PhilipLykov/LimeSDRCase/images/1778969445349.jpg

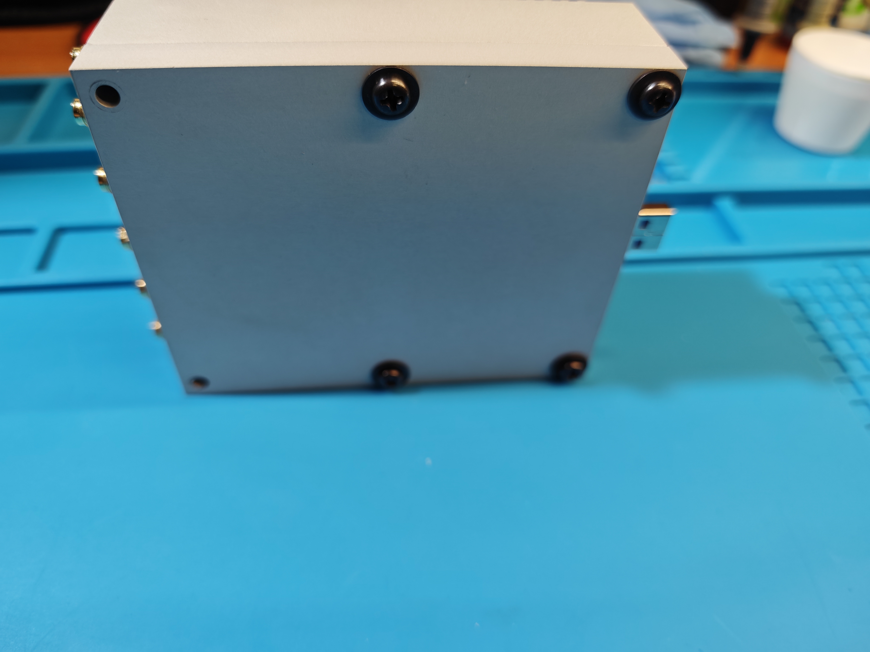
images/1778969445349.jpg
