PhilipLykov/LimeSDRCase/images/1778969445375.jpg

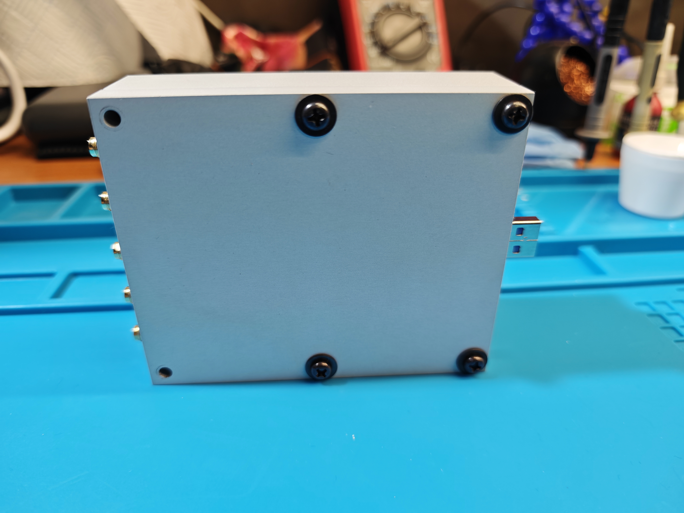
images/1778969445375.jpg
