PhilipLykov/LimeSDRCase/images/1778969445397.jpg

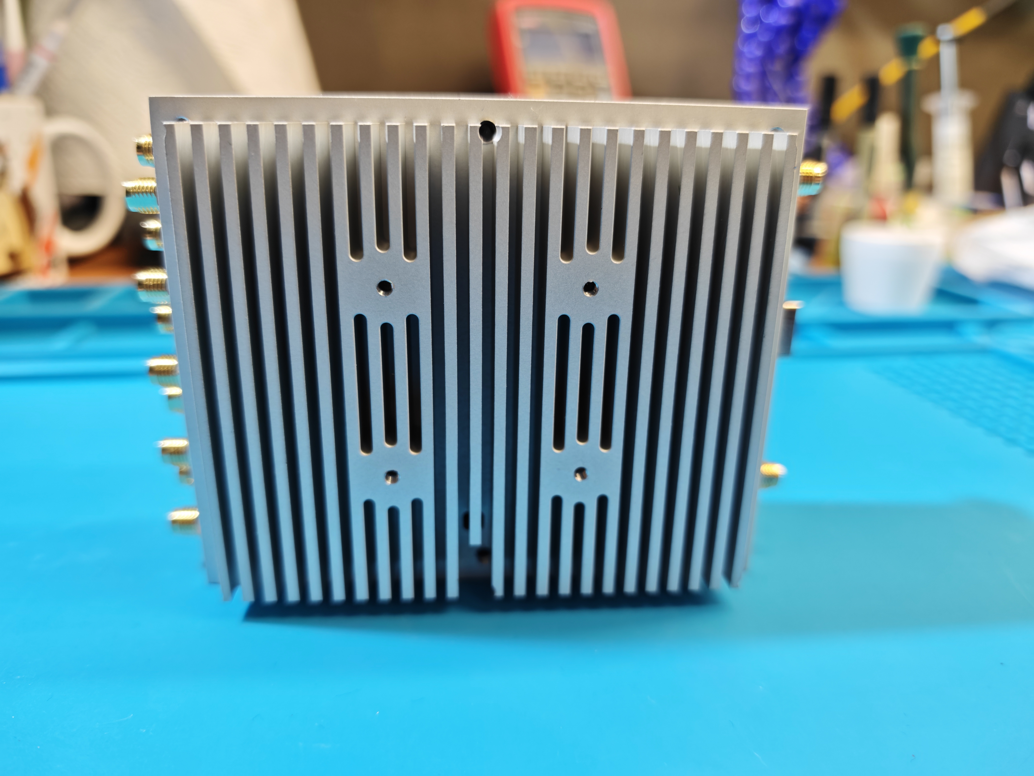
images/1778969445397.jpg
