PhilipLykov/LimeSDRCase/images/1778969445446.jpg

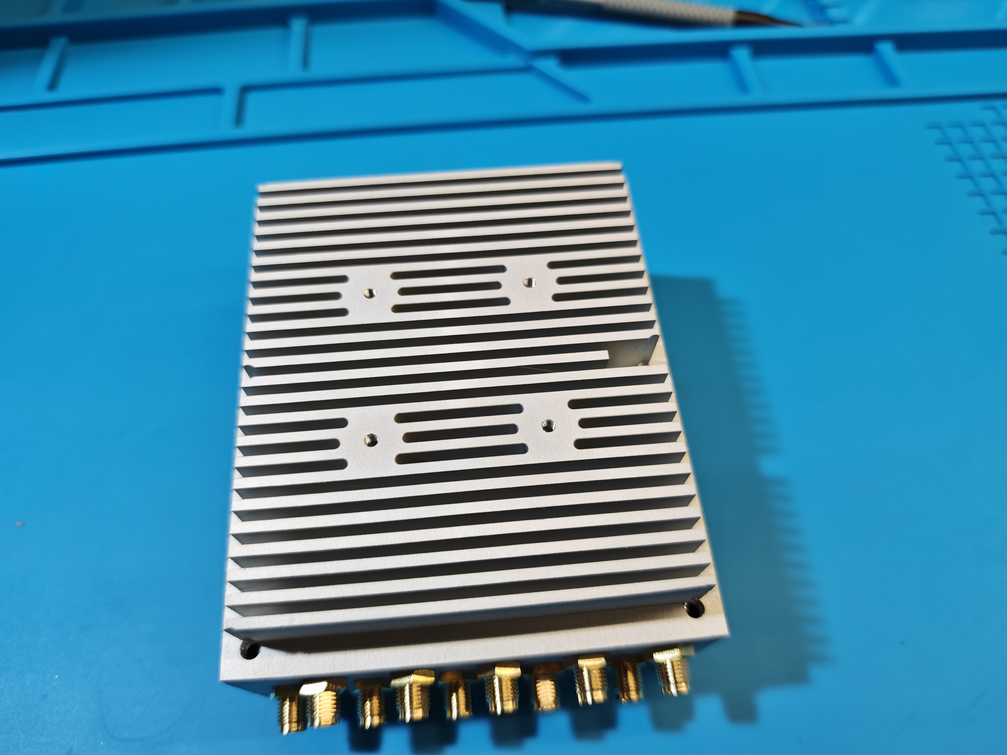
images/1778969445446.jpg
