PhilipLykov/LimeSDRCase/images/1778969445494.jpg

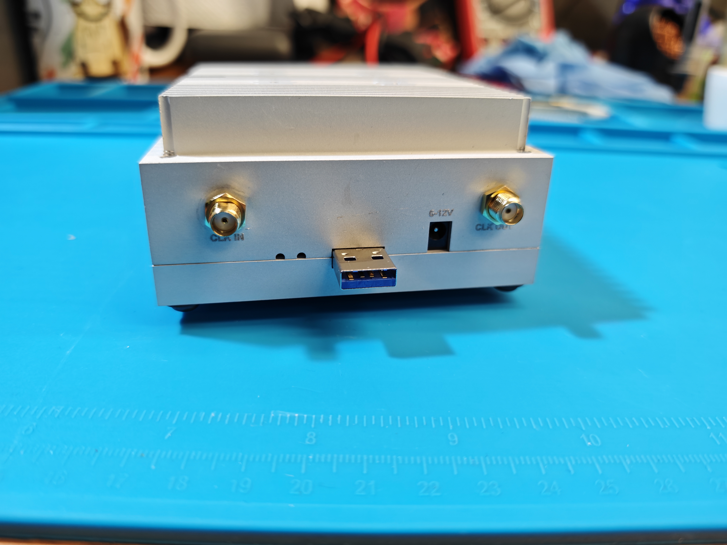
images/1778969445494.jpg
