PhilipLykov/LimeSDRCase/images/1778969445562.jpg

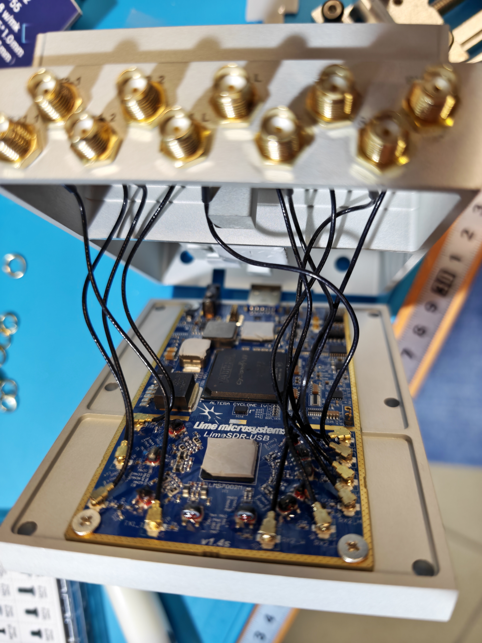
images/1778969445562.jpg
