PhilipLykov/LimeSDRCase/images/1778969445588.jpg

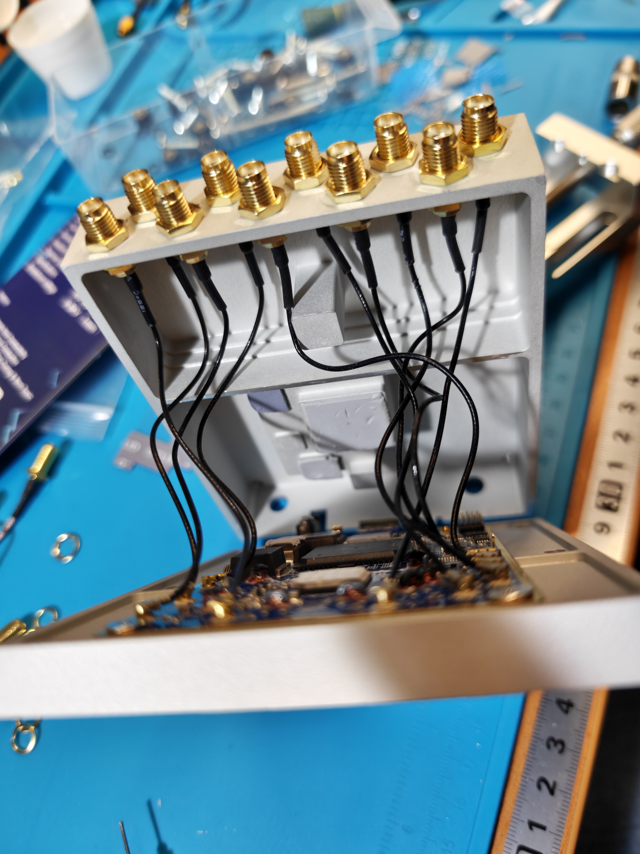
images/1778969445588.jpg
