PhilipLykov/LimeSDRCase/images/1778969445642.jpg

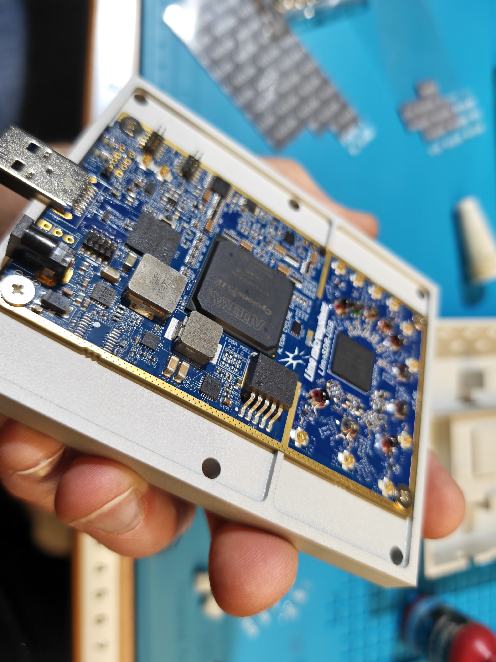
images/1778969445642.jpg
