PhilipLykov/LimeSDRCase/images/1778969445668.jpg

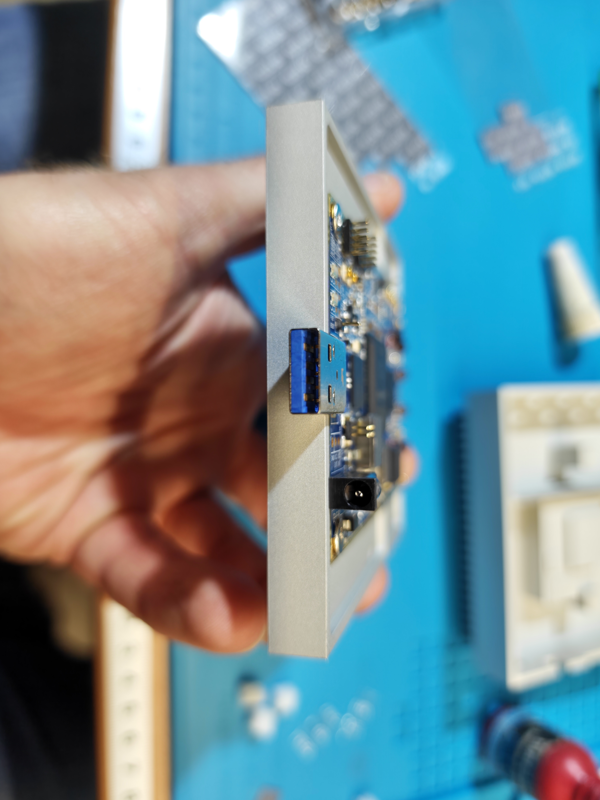
images/1778969445668.jpg
