PhilipLykov/LimeSDRCase/images/1778969445693.jpg

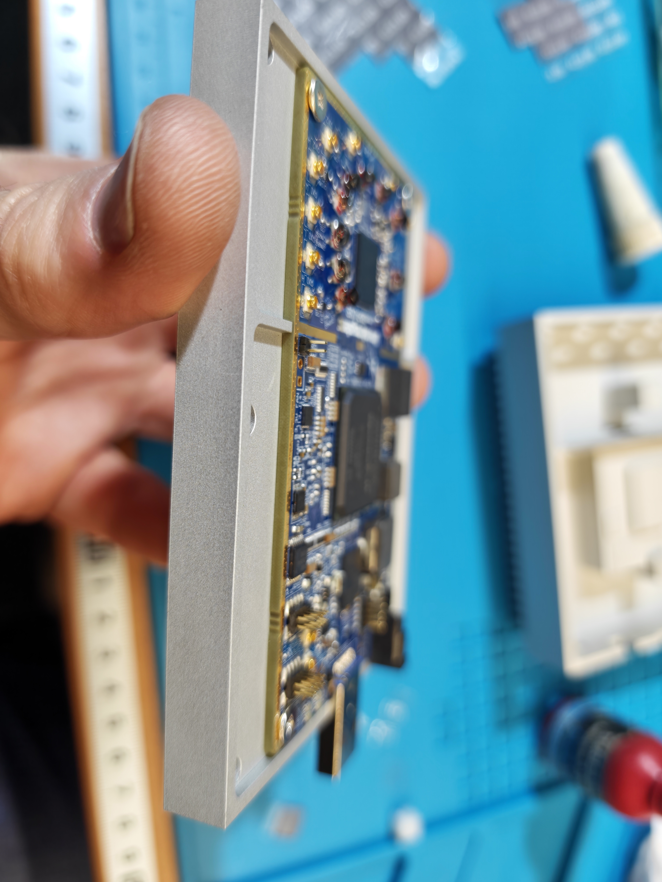
images/1778969445693.jpg
