PhilipLykov/LimeSDRCase/images/1778969445718.jpg

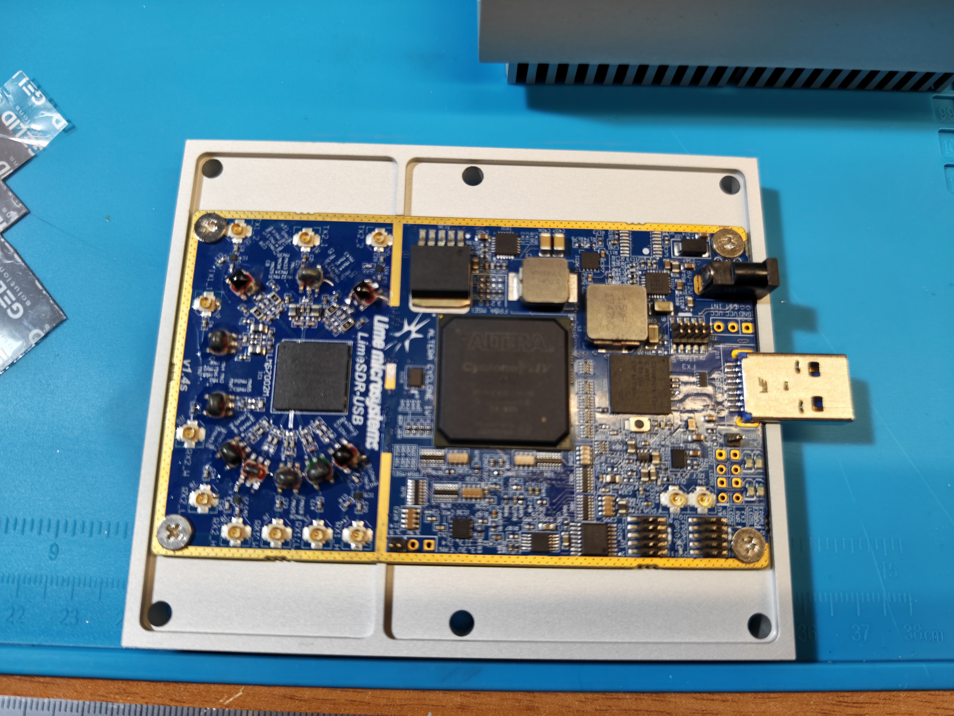
images/1778969445718.jpg
