PhilipLykov/LimeSDRCase/images/1778969445789.jpg

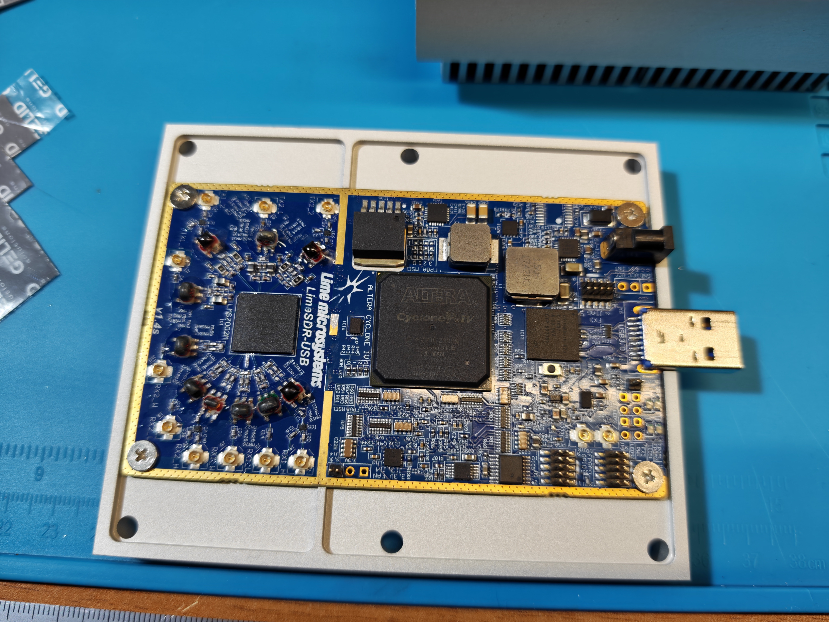
images/1778969445789.jpg
