PhilipLykov/LimeSDRCase/images/1778969445815.jpg

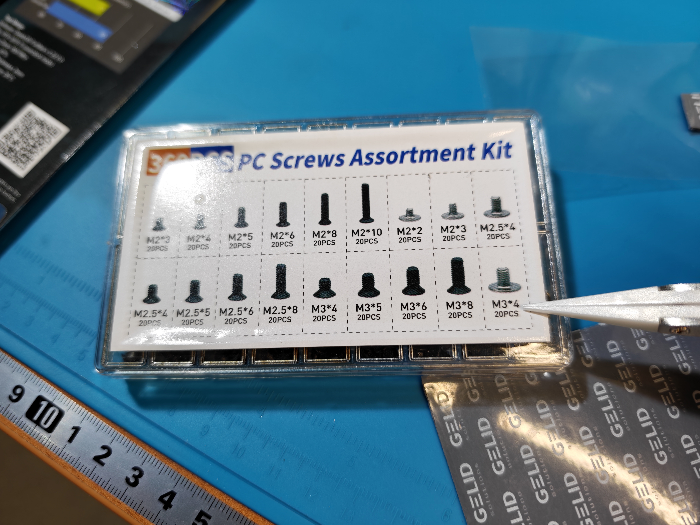
images/1778969445815.jpg
