PhilipLykov/LimeSDRCase/images/1778969445856.jpg

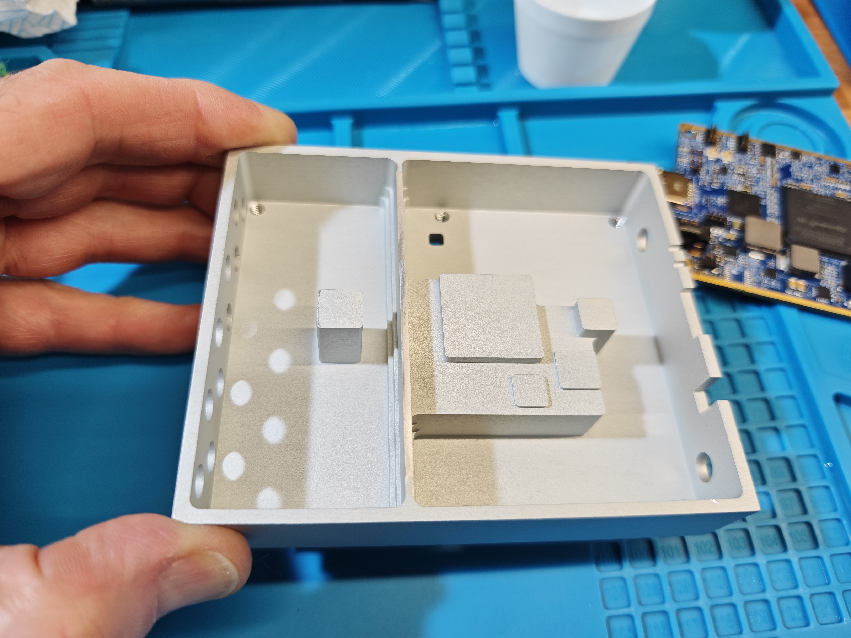
images/1778969445856.jpg
