PhilipLykov/LimeSDRCase/images/1778969445876.jpg

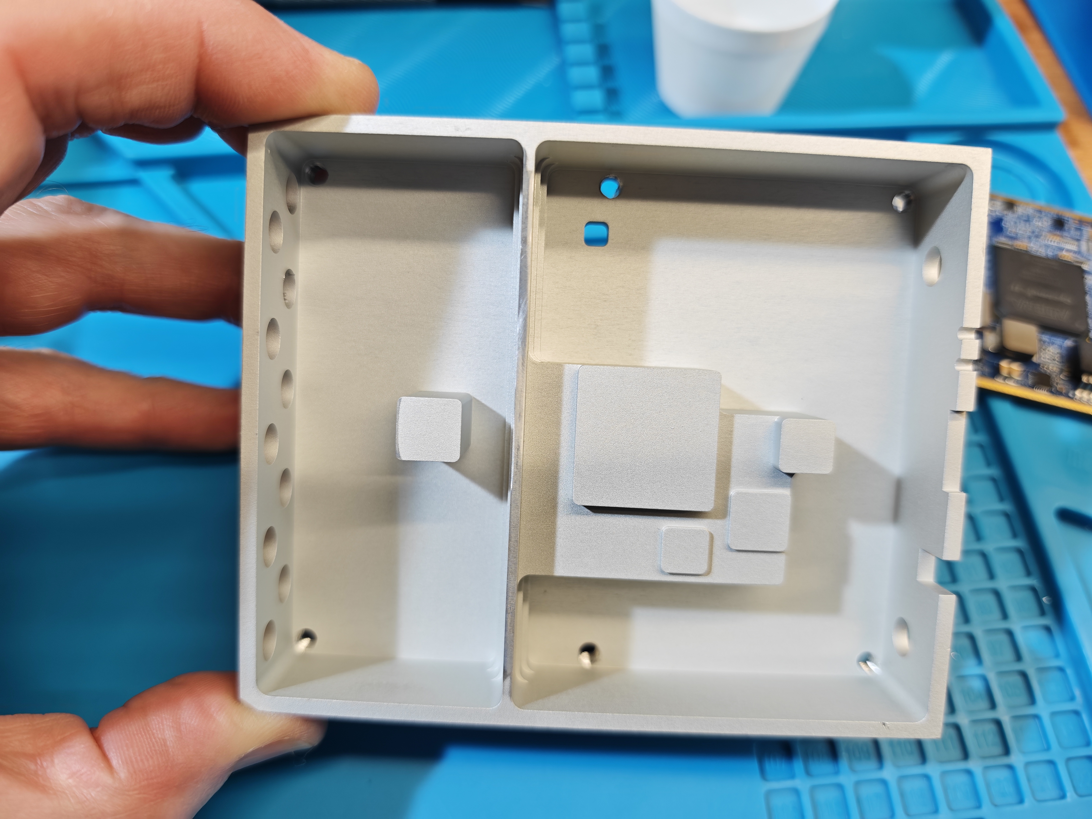
images/1778969445876.jpg
