PhilipLykov/LimeSDRCase/images/1778969445901.jpg

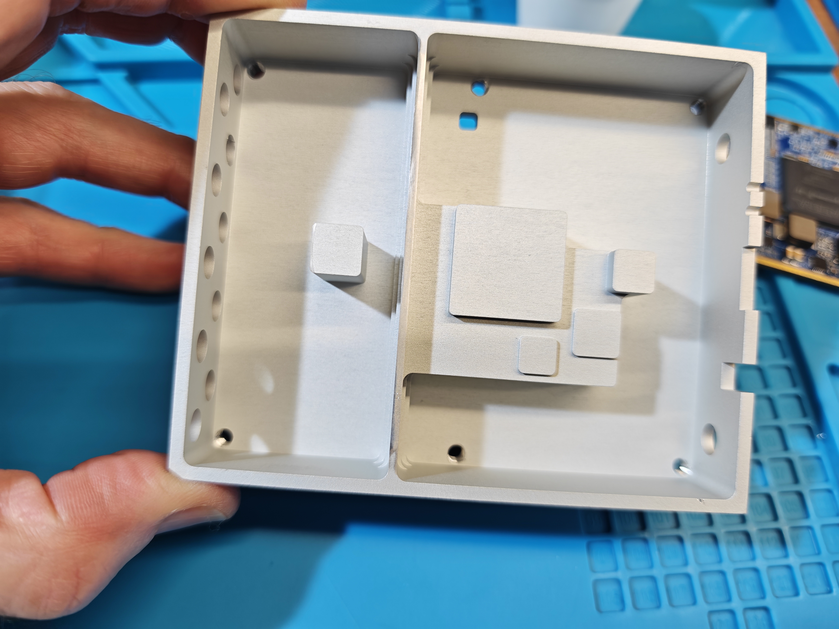
images/1778969445901.jpg
