PhilipLykov/LimeSDRCase/images/1778969445950.jpg

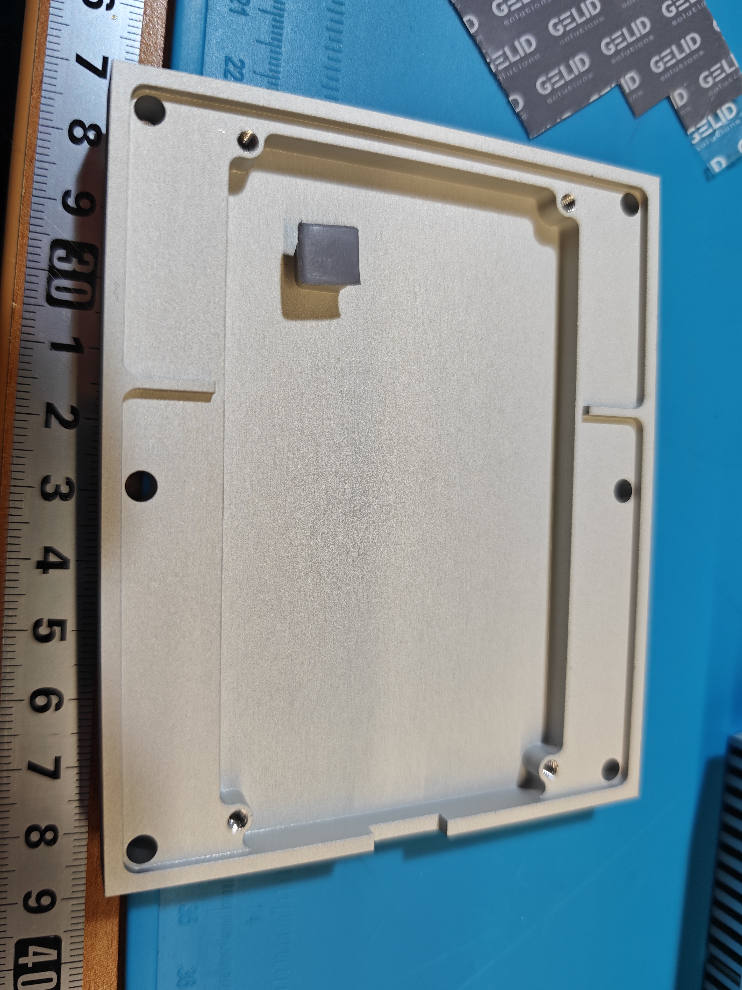
images/1778969445950.jpg
